dattasaurabh82/pi_pico_komorebi_bokeh_stick/main/engine.cpp

// engine.cpp — implementation. Sections: setup/deal, palette, surprise
// fade, announcements, and the per-frame render.
#include <Arduino.h>
#include "engine.h"
#include "render.h"

// ---------- randomness ----------

float KomorebiEngine::frand(float lo, float hi) {
  return lo + (hi - lo) * (random(10000) / 10000.0f);
}

// Stronger boot entropy than a single ADC read: stir 16 floating-pin
// samples with time. Gives a genuinely fresh constellation per press
// and per power cycle.
uint32_t KomorebiEngine::entropySeed() {
  uint32_t s = micros();
  for (int i = 0; i < 16; i++) {
    s = (s << 3) ^ (s >> 5) ^ (uint32_t)analogRead(A0) ^ (s * 2654435761u);
    delayMicroseconds(37 + (s & 63));
  }
  return s;
}

// ---------- lifecycle ----------

void KomorebiEngine::begin(DVIGFX8* display) {
  disp_ = display;
  fx::init();
  randomSeed(entropySeed());
  deal();
  // Every dapple starts fully melted-in; density gating happens per frame.
  for (int i = 0; i < N_MAX_DAPPLES; i++) d_[i].act = 1.0f;
  fade_ = 0.0f; fadeState_ = FadeState::In;   // every boot breathes in
}

// Deal all N_MAX dapples in three size classes (proportions from the
// 16-dapple original: 3 large pools / 5 mid / 8 small sparkles).
// Density only decides how many are SHOWN — dealt state covers the max.
void KomorebiEngine::deal() {
  const int nLarge = (N_MAX_DAPPLES * 3 + 8) / 16;
  const int nMidEnd = nLarge + (N_MAX_DAPPLES * 5 + 8) / 16;
  for (int i = 0; i < N_MAX_DAPPLES; i++) {
    float base;
    if (i < nLarge)       base = frand(110, 150);
    else if (i < nMidEnd) base = frand(65, 95);
    else                  base = frand(30, 50);
    float ecc = frand(-0.22f, 0.22f);         // squash one axis a bit
    d_[i].ow = (int)(base * (1.0f + ecc));
    d_[i].oh = (int)(base * (1.0f - ecc));
    d_[i].bx = frand(20, SCREEN_W - 20);
    d_[i].by = frand(20, SCREEN_H - 20);
    d_[i].ax1 = frand(3, 8);  d_[i].ay1 = frand(2, 6);
    d_[i].ax2 = frand(1, 4);  d_[i].ay2 = frand(1, 3);
    d_[i].f1 = frand(0.003f, 0.010f);         // 100-330 s: barely drifts
    d_[i].f2 = frand(0.008f, 0.025f);         // small tremble on top
    d_[i].p1 = frand(0, 6.283f); d_[i].p2 = frand(0, 6.283f);
    if (i < nMidEnd) { d_[i].bri = frand(0.40f, 0.80f); d_[i].bf = frand(0.010f, 0.030f); }
    else             { d_[i].bri = frand(0.25f, 0.55f); d_[i].bf = frand(0.025f, 0.060f); }
    d_[i].bp = frand(0, 6.283f);
    d_[i].sf = frand(0.006f, 0.020f);         // shape morph: 50-170 s
    d_[i].sp = frand(0, 6.283f);
    // act is NOT reset here: melt state carries across deals so a
    // surprise mid-density-change doesn't pop dapples.
  }
}

// ---------- palette ----------
// warmth01 blends between a cool near-white and a low amber by lerping
// the per-channel gain and gamma. shimmer (-1..+1) is the announcement:
// it briefly pushes warmth around its set point so the user SEES which
// parameter they just selected.
// gain: exposure. 1.0 = as designed; 1.3 lifts the mid-tones 30% (whites
// saturate a little earlier), 0.7 dims them. Black stays black.
// contrast01: 0 flattens the curve (gamma x0.8, lifted mids, overcast),
// 1 steepens it (gamma x1.2, punchier). 0.5 = the original curve.
void KomorebiEngine::buildPalette(float warmth01, float shimmer, float gain, float contrast01) {
  float w = warmth01 + shimmer * 0.20f;
  if (w < 0) w = 0; if (w > 1) w = 1;
  float gm = 0.8f + 0.4f * contrast01;   // gamma multiplier
  // endpoints: cool (w=0) .. warm (w=1)
  float rG = 255.0f,                 rE = 0.82f + w * (0.55f - 0.82f);
  float gG = 250.0f + w * (205.0f - 250.0f), gE = 0.84f + w * (0.88f - 0.84f);
  float bG = 240.0f + w * (110.0f - 240.0f), bE = 0.92f + w * (1.70f - 0.92f);
  for (int i = 0; i < 256; i++) {
    float t = i / 255.0f * gain;
    if (t > 1.0f) t = 1.0f;
    disp_->setColor(i, (uint8_t)(rG * powf(t, rE * gm)),
                       (uint8_t)(gG * powf(t, gE * gm)),
                       (uint8_t)(bG * powf(t, bE * gm)));
  }
}

// ---------- surprise + announcements ----------

void KomorebiEngine::startSurprise() {
  if (fadeState_ == FadeState::Idle) fadeState_ = FadeState::Out;
}

void KomorebiEngine::announce(Param p, float now_s) {
  announceParam_ = p;
  announceT0_ = now_s;
}

float KomorebiEngine::slew(float cur, float target, float maxStep) {
  float d = target - cur;
  if (d >  maxStep) d =  maxStep;
  if (d < -maxStep) d = -maxStep;
  return cur + d;
}

// ---------- per-frame ----------

void KomorebiEngine::renderFrame(float t, float dt, const Params& params) {
  // Surprise fade machine: breathe out -> fresh deal -> breathe in.
  if (fadeState_ == FadeState::Out) {
    fade_ -= dt / FADE_OUT_S;
    if (fade_ <= 0.0f) {
      fade_ = 0.0f;
      randomSeed(entropySeed());
      deal();
      fadeState_ = FadeState::In;
    }
  } else if (fadeState_ == FadeState::In) {
    fade_ += dt / FADE_IN_S;
    if (fade_ >= 1.0f) { fade_ = 1.0f; fadeState_ = FadeState::Idle; }
  } else if (fadeState_ == FadeState::SighOut) {
    fade_ -= dt / FADE_OUT_S;
    if (fade_ <= 0.0f) { fade_ = 0.0f; fadeState_ = FadeState::Dark; }
  }
  float fEased = fade_ * fade_ * (3.0f - 2.0f * fade_); // smooth breathe

  // Sky: slide the applied offsets toward their targets (full swing over
  // SKY_SLEW_S), then form the effective parameters the frame will use.
  sky_.warmth   = slew(sky_.warmth,   skyTarget_.warmth,   dt * SKY_RANGE_WARMTH   / SKY_SLEW_S);
  sky_.breeze   = slew(sky_.breeze,   skyTarget_.breeze,   dt * SKY_RANGE_BREEZE   / SKY_SLEW_S);
  sky_.density  = slew(sky_.density,  skyTarget_.density,  dt * SKY_RANGE_DENSITY  / SKY_SLEW_S);
  sky_.exposure = slew(sky_.exposure, skyTarget_.exposure, dt * SKY_RANGE_EXPOSURE / SKY_SLEW_S);
  sky_.contrast = slew(sky_.contrast, skyTarget_.contrast, dt * SKY_RANGE_CONTRAST / SKY_SLEW_S);
  effWarmth_  = (int)(params.warmth  + sky_.warmth  + 0.5f); if (effWarmth_  < 0) effWarmth_ = 0;  if (effWarmth_  > 100) effWarmth_  = 100;
  effBreeze_  = (int)(params.breeze  + sky_.breeze  + 0.5f); if (effBreeze_  < 0) effBreeze_ = 0;  if (effBreeze_  > 100) effBreeze_  = 100;
  effDensity_ = (int)(params.density + sky_.density + 0.5f); if (effDensity_ < DENSITY_MIN) effDensity_ = DENSITY_MIN; if (effDensity_ > DENSITY_MAX) effDensity_ = DENSITY_MAX;
  effContrast_= (int)(params.contrast+ sky_.contrast + 0.5f); if (effContrast_ < 0) effContrast_ = 0; if (effContrast_ > 100) effContrast_ = 100;
  float c01 = effContrast_ / 100.0f;
  // Contrast on the pools: flat = bigger and dimmer (diffuse light),
  // crisp = smaller and brighter. Area/brightness product stays roughly put.
  float sizeM = 1.25f - 0.5f * c01;      // 1.25 .. 0.75
  float briM  = 0.80f + 0.40f * c01;     // 0.80 .. 1.20
  float gain = 1.0f + sky_.exposure;
  int gainQ = (int)(gain * 100.0f);

  // Announcement envelope: 1 at click, decaying to 0 over ANNOUNCE_S.
  float aU = (t - announceT0_) / ANNOUNCE_S;
  float aEnv = (aU >= 0.0f && aU < 1.0f) ? (1.0f - aU) : 0.0f;

  // Palette: DVIGFX8 keeps one palette per buffer, so any change must be
  // written on TWO consecutive frames (once per back buffer) or the image
  // strobes between the new palette and stale/garbage data.
  bool shimmering = (aEnv > 0.0f) && (announceParam_ == Param::Warmth);
  if (effWarmth_ != lastWarmth_ || gainQ != lastGainQ_ || effContrast_ != lastContrast_) {
    palFrames_ = 2; lastWarmth_ = effWarmth_; lastGainQ_ = gainQ; lastContrast_ = effContrast_;
  }
  if (shimmering) palFrames_ = 2;   // animating: keep writing (+2 to settle)
  if (palFrames_ > 0) {
    float shimmer = shimmering ? sinf(aU * 6.283f * 1.5f) * aEnv : 0.0f;
    buildPalette(effWarmth_ / 100.0f, shimmer, gain, c01);
    palFrames_--;
  }

  // Breeze scaling: one scalar drives amplitudes, wind, and breath rate.
  float b01 = effBreeze_ / 100.0f;
  float amp = 0.3f + 2.2f * b01;      // positional sway multiplier
  float rate = 0.6f + 1.2f * b01;     // breathing tempo multiplier
  // Breeze announcement = one extra gust pushed through the wind term.
  float gust = (announceParam_ == Param::Breeze) ? aEnv * 1.6f : 0.0f;
  float wind = (sinf(t * 0.020f) + 0.5f * sinf(t * 0.053f + 1.7f)) * amp
               + gust * sinf(aU * 3.14159f);

  uint8_t* buf = disp_->getBuffer();
  memset(buf, 0, SCREEN_W * SCREEN_H);

  for (int i = 0; i < N_MAX_DAPPLES; i++) {
    Dapple& dp = d_[i];
    // Density melt: ramp activation toward shown/hidden, render if lit.
    float target = (i < effDensity_) ? 1.0f : 0.0f;
    if (dp.act < target)      { dp.act += dt * ACT_RAMP_PER_S; if (dp.act > 1) dp.act = 1; }
    else if (dp.act > target) { dp.act -= dt * ACT_RAMP_PER_S; if (dp.act < 0) dp.act = 0; }
    if (dp.act <= 0.01f) continue;

    // Sway scaled by breeze (amp); breath tempo scaled by breeze (rate).
    float x = dp.bx + (dp.ax1 * sinf(t * dp.f1 * 6.283f + dp.p1)
                     + dp.ax2 * sinf(t * dp.f2 * 6.283f + dp.p2)) * amp
                    + 2.0f * wind;
    float y = dp.by + (dp.ay1 * cosf(t * dp.f1 * 5.1f + dp.p2)
                     + dp.ay2 * sinf(t * dp.f2 * 7.3f + dp.p1)) * amp;
    float br = dp.bri * (0.55f + 0.35f * sinf(t * dp.bf * 6.283f * rate + dp.bp)
                                - 0.12f * wind * wind * 0.25f);
    if (br < 0.05f) br = 0.05f;

    // Density announcement: the first dapple blinks out and back once.
    float blink = 1.0f;
    if (announceParam_ == Param::Density && aEnv > 0.0f && i == 0) {
      blink = 1.0f - sinf(aU * 3.14159f); // dip to 0 mid-announcement
    }

    // Contrast announcement: every pool briefly tightens and brightens.
    float sharpen = (announceParam_ == Param::Contrast && aEnv > 0.0f) ? sinf(aU * 3.14159f) : 0.0f;
    float sM = sizeM * (1.0f - 0.25f * sharpen);
    float bM = briM  * (1.0f + 0.30f * sharpen);

    // Shape breathing: slow area-preserving squash/stretch.
    float m = 1.0f + 0.06f * sinf(t * dp.sf * 6.283f + dp.sp);
    int bs = (int)(br * bM * fEased * dp.act * blink * 256);
    if (bs > 255) bs = 255;
    fx::blitAddScaled(buf, (int)x, (int)y, bs,
                      (int)(dp.ow * m * sM), (int)(dp.oh / m * sM));
  }
  fx::vignettePass(buf);
}
